sboysel/giraffe36/output/pcbs/routed/giraffe36_pcb_routed_back.jpg

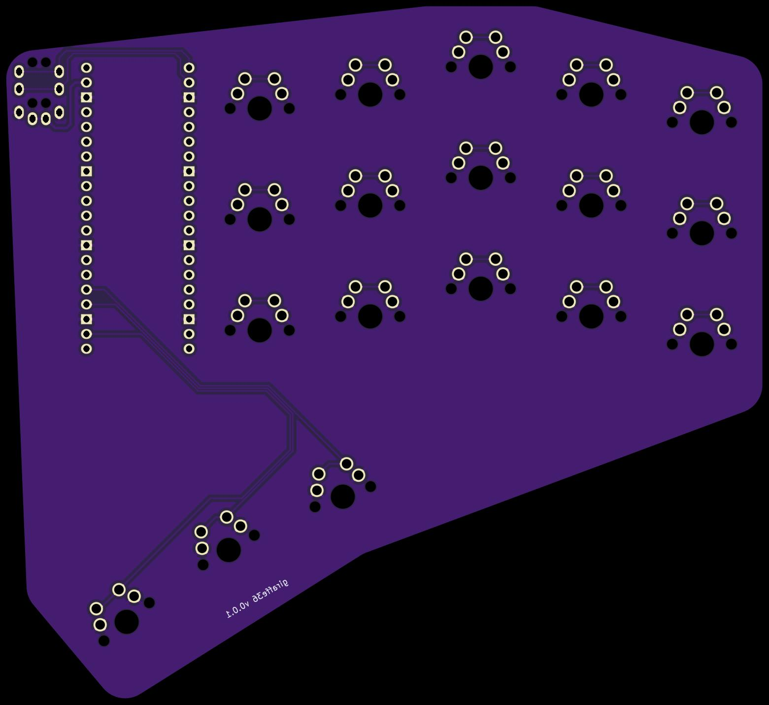
output/pcbs/routed/giraffe36_pcb_routed_back.jpg
