sboysel/giraffe36/output/pcbs/routed/giraffe36_pcb_routed_front.jpg

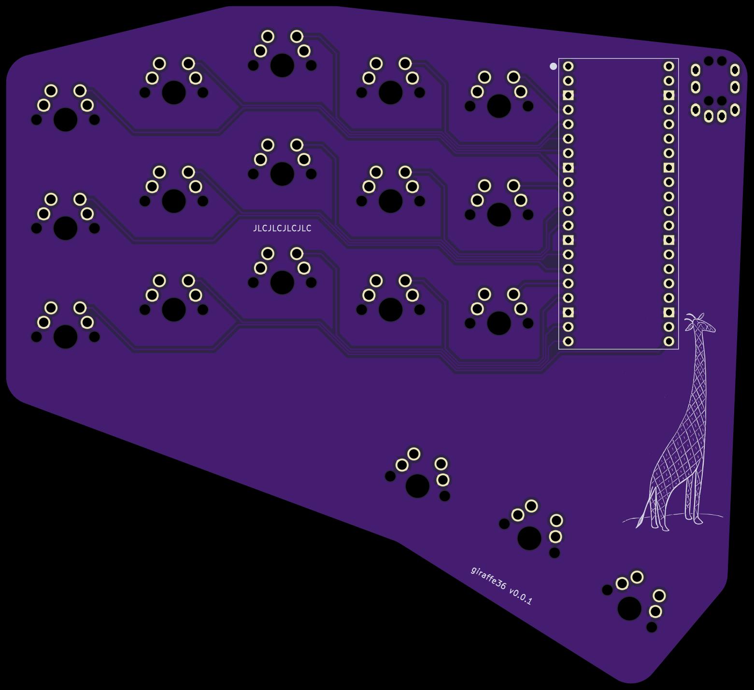
output/pcbs/routed/giraffe36_pcb_routed_front.jpg
